alexmlucas/i1/control_surface/Parameter.h

#ifndef PARAMETER
#define PARAMETER

struct Parameter
{
    int value;
    char character;
    //void (*callback_function)(Menu_Controller*);
    //void set_callback_func(void (*f)(Menu_Controller*)) {callback_function = f;};
};

#endif
