alexmlucas/i1/rpi_script/parameter_manager.py

import serial
import csv
from subprocess import call

class Parameter_Manager:

	def __init__(self, port, baud_rate):
		self.port = port
		self.baud_rate = baud_rate
		self.song_data_path = "/home/pi/i1/rpi_script/song_data.txt"
		self.global_data_path = "/home/pi/i1/rpi_script/global_data.txt"
		
		# Initalise class variables from saved parameter values
		self.current_song = self.get_global_parameter('b')
		self.master_level = self.float_value_generator(self.get_global_parameter('a'))
		self.backing_level = self.float_value_generator(self.get_song_parameter('e'))
		self.guitar_level = self.midi_value_generator(self.get_song_parameter('d'))
		
		# Intialise serial port
		self.control_board = serial.Serial(self.port, self.baud_rate, timeout = 0.1)
		
		# Flush inputs and outputs
		self.control_board.flushInput()
		self.control_board.flushOutput()
		 
		# Flag for indicating that bluetooth reconnection has been requested.
		# Initialise with a value of True to ensure wristband connection is attempted on program start.
		self.reconnect_wristband_flag = True
	
	def midi_value_generator(self, value_to_convert):
		# convert values between 0 - 10 to vaues between 0 - 127
		return (value_to_convert / 10) * 127
		
	def float_value_generator(self, value_to_convert):
		return value_to_convert / 10
	
	def set_song_player(self, song_player):
		# Create a local reference to the song player.
		self.song_player = song_player
		# Now that a reference to the song player is available, set the song...
		self.song_player.set_song(self.get_global_parameter('b'))
		# ...and set its level
		self.song_player.set_level(self.backing_level * self.master_level)
		
	def set_guitar(self, guitar):
		# Create a local reference to the guitar.
		self.guitar = guitar
		# Now that a reference to the guitar is available, set its path...
		self.guitar.set_sound_font(self.get_song_parameter('c'))
		# ... and its level
		self.guitar.set_level(int(self.guitar_level * self.master_level))
		
		#### Set scales ####
		# Red scale
		self.guitar.set_zone_notes(0, self.get_song_parameter('f'))
		# Green scale
		self.guitar.set_zone_notes(1, self.get_song_parameter('g'))
		# Blue scale
		self.guitar.set_zone_notes(2, self.get_song_parameter('h'))
		
		#### Set transpositions ####
		# Red transposition
		self.guitar.set_transposition(0, self.get_song_parameter('i'))
		# Green transposition
		self.guitar.set_transposition(1, self.get_song_parameter('j'))
		# Blue transposition
		self.guitar.set_transposition(2, self.get_song_parameter('k'))
	
	def check_incoming(self):
		# Read data from the serial port
		incoming_serial = self.control_board.readline().rstrip().decode()
		
		# Flush the serial port
		self.control_board.flushInput()
		
		if incoming_serial:
			print(incoming_serial)
			
			if incoming_serial[0] is 'a':
				# Master level (Global Parameter)
				
				# Convert incoming string to a float value 
				value_as_float = self.float_value_generator(self.get_number_from_string(incoming_serial))
				
				# Set the master level
				self.master_level = value_as_float
				# Change the level of the song player
				self.song_player.set_level(self.backing_level * self.master_level)
				# Change the level of the guitar
				self.guitar.set_level(int(self.guitar_level * self.master_level))
				
				# Write the parameter
				self.write_global_parameter(incoming_serial)
				
			elif incoming_serial[0] is 'b':
				# Song (Global Parameter)
				
				# Write the parameter
				self.write_global_parameter(incoming_serial)
				
				# Update the current song
				self.current_song = int(incoming_serial[2])
				
				# Update local variables
				self.backing_level = self.float_value_generator(self.get_song_parameter('e'))
				self.guitar_level = self.midi_value_generator(self.get_song_parameter('d'))
				
				# Act on changes to parameter values
				self.song_player.set_song(self.current_song)
				self.song_player.set_level(self.backing_level * self.master_level)
				self.guitar.set_level(int(self.guitar_level * self.master_level))
				self.guitar.set_sound_font(self.get_song_parameter('c'))
				self.guitar.set_zone_notes(0, self.get_song_parameter('f'))
				self.guitar.set_zone_notes(1, self.get_song_parameter('g'))
				self.guitar.set_zone_notes(2, self.get_song_parameter('h'))
				self.guitar.set_transposition(0, self.get_song_parameter('i'))
				self.guitar.set_transposition(1, self.get_song_parameter('j'))
				self.guitar.set_transposition(2, self.get_song_parameter('k'))
				
				# Transmit the song data
				self.song_data_requested()
				
			elif incoming_serial[0] is 'c':
				# Guitar
				# Set the sound font by removing the first two characters from the incoming serial string and converting to int
				self.guitar.set_sound_font(int(incoming_serial[1:]))
				# Write the parameter
				self.write_song_parameter(incoming_serial)
				
			elif incoming_serial[0] is 'd':
				# Guitar Level

				# convert incoming string to midi value 
				midi_value = self.midi_value_generator(self.get_number_from_string(incoming_serial))
				# Set the backing level local value
				self.guitar_level = midi_value
				# actually change the volume
				self.guitar.set_level(int(self.guitar_level * self.master_level))
				
				# Write the parameter
				self.write_song_parameter(incoming_serial)
				
			elif incoming_serial[0] is 'e':
				# Backing Level
				
				# convert incoming string to float value 
				value_as_float = self.float_value_generator(self.get_number_from_string(incoming_serial))
				# Set the backing level local value
				self.backing_level = value_as_float
				# actually change the volume
				self.song_player.set_level(self.backing_level * self.master_level)
				
				# Write the parameter
				self.write_song_parameter(incoming_serial)	
				
			elif incoming_serial[0] is 'f':
				# Red Scale
				
				# Get the scale value
				scale_value = int(incoming_serial[2]) + (int(incoming_serial[1]) * 10)
				# Set the scale
				self.guitar.set_zone_notes(0, scale_value)

				# Write the parameter
				self.write_song_parameter(incoming_serial)	
					
			elif incoming_serial[0] is 'g':
				# Green Scale
				
				# Get the scale value
				scale_value = int(incoming_serial[2]) + (int(incoming_serial[1]) * 10)
				# Set the scale
				self.guitar.set_zone_notes(1, scale_value)

				# Write the parameter
				self.write_song_parameter(incoming_serial)			
				
			elif incoming_serial[0] is 'h':
				# Blue Scale
				
				# Get the scale value
				scale_value = int(incoming_serial[2]) + (int(incoming_serial[1]) * 10)
				# Set the scale
				self.guitar.set_zone_notes(2, scale_value)

				# Write the parameter
				self.write_song_parameter(incoming_serial)	
			
			elif incoming_serial[0] is 'i':
				# Red Root
				
				# Get the value
				transposition_value = int(incoming_serial[2]) + (int(incoming_serial[1]) * 10)
				# Set the scale
				self.guitar.set_transposition(0, transposition_value)

				# Write the parameter
				self.write_song_parameter(incoming_serial)	

			elif incoming_serial[0] is 'j':
				# Green Root
				
				# Get the value
				transposition_value = int(incoming_serial[2]) + (int(incoming_serial[1]) * 10)
				# Set the scale
				self.guitar.set_transposition(1, transposition_value)

				# Write the parameter
				self.write_song_parameter(incoming_serial)		
				
			elif incoming_serial[0] is 'k':
				# Blue Root
				
				# Get the value
				transposition_value = int(incoming_serial[2]) + (int(incoming_serial[1]) * 10)
				# Set the scale
				self.guitar.set_transposition(2, transposition_value)

				# Write the parameter
				self.write_song_parameter(incoming_serial)		
			
			elif incoming_serial[0] is 'l':
				# Zone
				# Write the parameter
				self.write_song_parameter(incoming_serial)	
			
			elif incoming_serial[0] is 'm':
				# Reconnect Request
				self.reconnect_wristband_flag = True
			
			elif incoming_serial[0] is 'n':
				# Power
				# Local action
				self.shutdown_device(incoming_serial)

			elif incoming_serial[0] is 'o':
				# Play
				self.song_player.set_play_state(int(incoming_serial[2]))
				
			elif incoming_serial[0] is 'r':
				# Initial data request.
				# Send the global parameters
				self.global_data_requested()
				
				# Send the song data
				self.song_data_requested()
				
	def shutdown_device(self, incoming_serial):
		print('Shutting down')
		#call("sudo shutdown -h now", shell=True)
		
	def write_song_parameter(self, incoming_serial):
		# Indicates whether or not a parameter has been found in the list.
		write_flag = False
		# Creates a list containing 5 lists, each of 8 items, all set to 0
		w, h = 4, 9;
		song_data_as_list = [[0 for x in range(w)] for y in range(h)] 
		
		'''print("before data added")
		with open('song_data.txt') as csv_file:
			song_data = csv.reader(csv_file, delimiter = ',')
			
			for row in song_data:
				print(row[current_song])'''
		
		with open(self.song_data_path) as csv_file:
			song_data_reader = csv.reader(csv_file, delimiter = ',')
			# Convert the song data to a list so that we can easily work with it.
			song_data_as_list = list(song_data_reader)
			
			# Initialise an index variable for use with the following for loop
			index = 0
			
			# Interate through the song data list 
			for index, row in enumerate(song_data_as_list):
				# Isolate the parameter associated with the currently selected song
				cell_string = row[self.current_song]
				
				# If the first character matches that of the incoming serial...
				if(incoming_serial[0] == cell_string[0]):
					#... indicate that we need to overwrite the parameter in this position.
					write_flag = True
					break
			
			# If the write flag is true...
			if write_flag == True:
				#... overwrite the parameter in the array.
				song_data_as_list[index][self.current_song] = incoming_serial
			
				# and write the data to the song data text file.
				with open(self.song_data_path, mode='w') as csv_file:
					song_data_writer = csv.writer(csv_file, delimiter = ',')
					song_data_writer.writerows(song_data_as_list)
			
		'''print("after data added")
		with open('song_data.txt') as csv_file:
			song_data = csv.reader(csv_file, delimiter = ',')
			
			for row in song_data:
				print(row[current_song])'''

	def write_global_parameter(self, incoming_serial):
		# Indicates whether or not a parameter has been found in the list.
		write_flag = False
		# Create a 2 x 1 array, initialised to 0
		w, h = 2, 1;
		global_data_as_list = [[0 for x in range(w)] for y in range(h)] 
		
		'''print("before data added")
		with open('global_data.txt') as csv_file:
			global_data_reader = csv.reader(csv_file, delimiter = ',')
			global_data_as_list = list(global_data_reader)
			print(global_data_as_list)'''
		
		with open(self.global_data_path) as csv_file:
			global_data_reader = csv.reader(csv_file, delimiter = ',')
			# Convert the global data to a list so that we can easily work with it.
			global_data_as_list = list(global_data_reader)
			
			# initialise index's for iterating through the following for loop.
			row_index = 0
			cell_index = 0
			
			for row_index, row in enumerate(global_data_as_list):
				
				for cell_index, cell_string in enumerate(row):
					# If the first character matches that of the incoming serial...
					if(incoming_serial[0] == cell_string[0]):
						#... indicate that we need to overwrite the parameter in this position.
						write_flag = True
						break
				
				# Exit the parent for loop
				if(write_flag == True):
					break
			
			# If the write flag is true...
			if write_flag == True:
				#... overwrite the parameter in the array.
				global_data_as_list[row_index][cell_index] = incoming_serial
				
			# and write the data to the song data text file.	
			with open(self.global_data_path, mode='w') as csv_file:
				global_data_writer = csv.writer(csv_file, delimiter = ',')
				global_data_writer.writerows(global_data_as_list)
			
			'''print("after data added")
			with open('global_data.txt') as csv_file:
				global_data_reader = csv.reader(csv_file, delimiter = ',')
				global_data_as_list = list(global_data_reader)
				print(global_data_as_list)'''
	
	def global_data_requested(self):
		with open(self.global_data_path) as csv_file:
			global_data = csv.reader(csv_file, delimiter = ',')
			
			# Nasty hack to get global data sent.
			# Will need to be changed if more data is added to the text file
			for row in global_data:
				byte_array = bytes(row[0], 'utf-8')
				self.control_board.write(byte_array)
				
				byte_array = bytes(row[1], 'utf-8')
				self.control_board.write(byte_array)
	
	
	
	def song_data_requested(self):
		with open(self.song_data_path) as csv_file:
			song_data = csv.reader(csv_file, delimiter = ',')
			
			for row in song_data:
				byte_array = bytes(row[self.current_song], 'utf-8')
				byte_array1 = row[self.current_song]				
				print(byte_array1)
				self.control_board.write(byte_array1.encode())
				
	'''def get_last_selected_song(self):
		# create a 2 x 1 array
		w, h = 2, 1;
		global_data_as_list = [[0 for x in range(w)] for y in range(h)] 
	
		with open('global_data.txt') as csv_file:
			global_data_reader = csv.reader(csv_file, delimiter = ',')
			
			global_data_as_list = list(global_data_reader)
			
			row_index = 0
			cell_index = 0
			
			for row_index, row in enumerate(global_data_as_list):
				for cell_index, cell_string in enumerate(row):
					if(cell_string[0] == 'b'):
						# song parameter found
						return int(cell_string[2])'''
	
	def get_global_parameter(self, parameter_character):
		# create a 2 x 1 array
		w, h = 2, 1;
		global_data_as_list = [[0 for x in range(w)] for y in range(h)] 
	
		with open(self.global_data_path) as csv_file:
			global_data_reader = csv.reader(csv_file, delimiter = ',')
			
			global_data_as_list = list(global_data_reader)
			
			row_index = 0
			cell_index = 0
			
			for row_index, row in enumerate(global_data_as_list):
				for cell_index, cell_string in enumerate(row):
					# If the first character matches...
					if(parameter_character == cell_string[0]):
						#... return the value
						return int(cell_string[2]) + (int(cell_string[1]) * 10)
						
						
	def get_song_parameter(self, parameter_character):
		# Indicates whether or not a parameter has been found in the list.
		write_flag = False
		# Creates a list containing 5 lists, each of 8 items, all set to 0
		w, h = 4, 9;
		song_data_as_list = [[0 for x in range(w)] for y in range(h)] 
		
		'''print("before data added")
		with open('song_data.txt') as csv_file:
			song_data = csv.reader(csv_file, delimiter = ',')
			
			for row in song_data:
				print(row[current_song])'''
		
		with open(self.song_data_path) as csv_file:
			song_data_reader = csv.reader(csv_file, delimiter = ',')
			# Convert the song data to a list so that we can easily work with it.
			song_data_as_list = list(song_data_reader)
			
			# Initialise an index variable for use with the following for loop
			index = 0
			
			# Interate through the song data list 
			for index, row in enumerate(song_data_as_list):
				# Isolate the parameter associated with the currently selected song
				cell_string = row[self.current_song]
				
				# If the first character matches...
				if(parameter_character == cell_string[0]):
					#... return the value
					return int(cell_string[2]) + (int(cell_string[1]) * 10)
	
	def get_number_from_string(self, string_value):
		return int(string_value[2]) + (int(string_value[1]) * 10)
		
	def tx_wristband_connection_attempt(self):
		character_to_transmit = 'p00'
		self.control_board.write(character_to_transmit.encode())
		
	def tx_wristband_success(self):
		character_to_transmit = 'q00'
		self.control_board.write(character_to_transmit.encode())
		
	def tx_wristband_failure(self):
		character_to_transmit = 'r00'
		self.control_board.write(character_to_transmit.encode())
	
